daniel-hauser/homelab-rack/renders/beds/bed_6.png

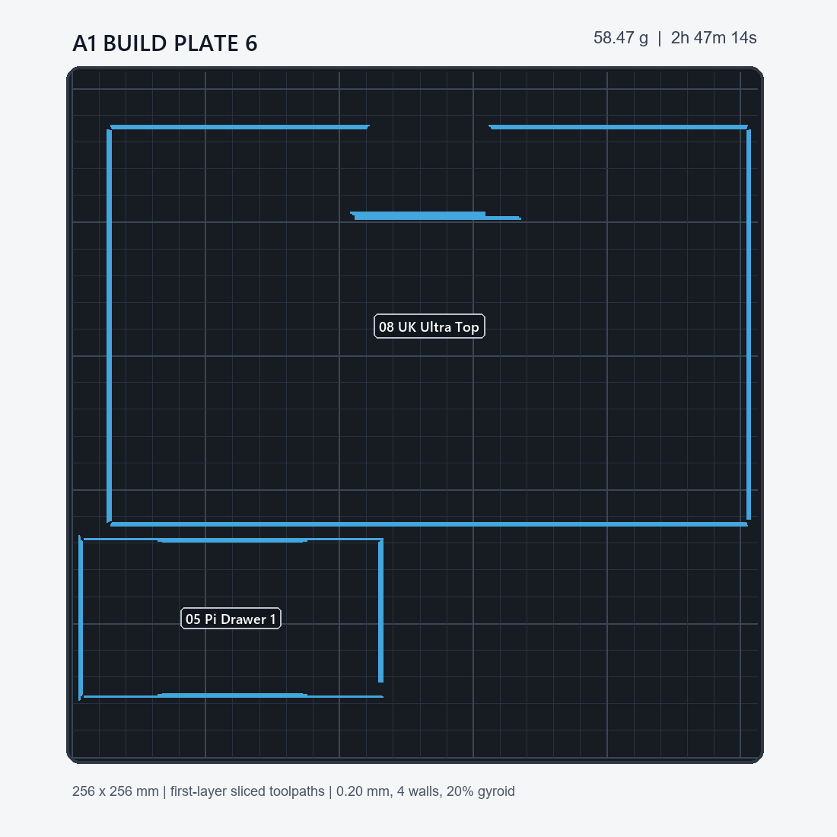
renders/beds/bed_6.png
