daniel-hauser/homelab-rack/renders/modular_bay_preview_final.png

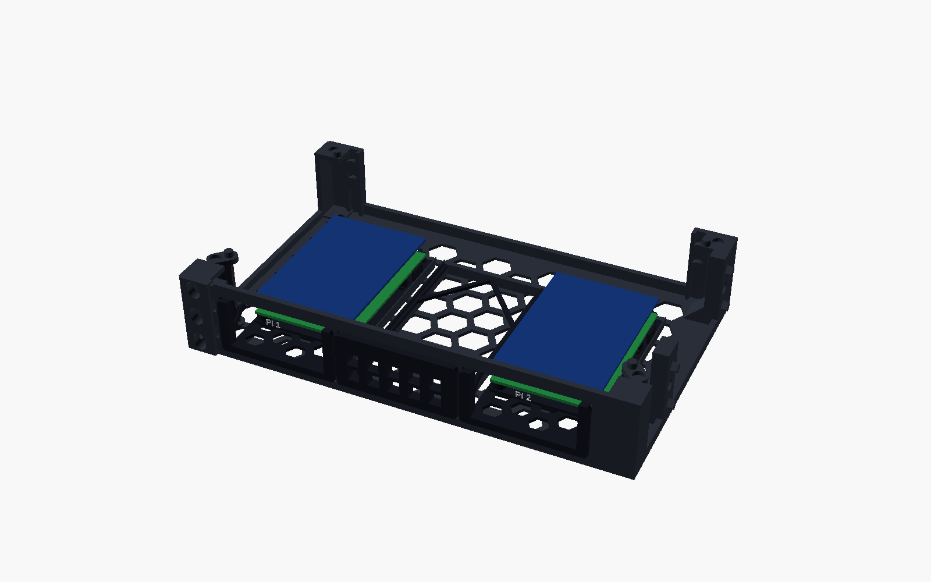
renders/modular_bay_preview_final.png
