daniel-hauser/homelab-rack/renders/rack_preview_final.png

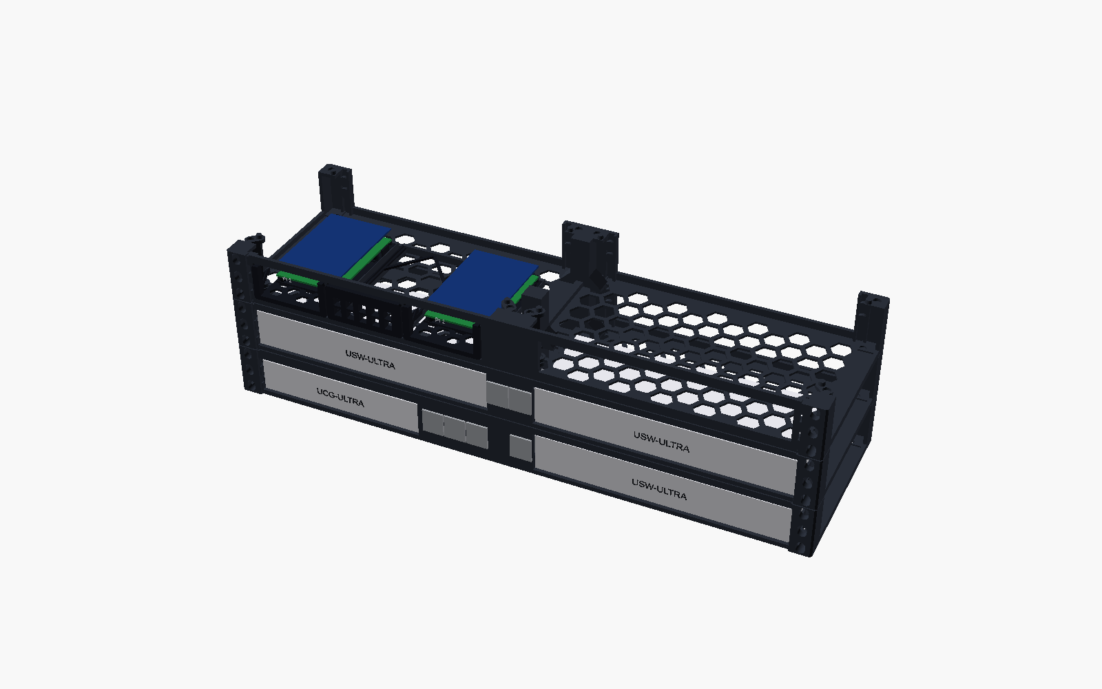
renders/rack_preview_final.png
