daniel-hauser/homelab-rack/renders/side_join_preview.png

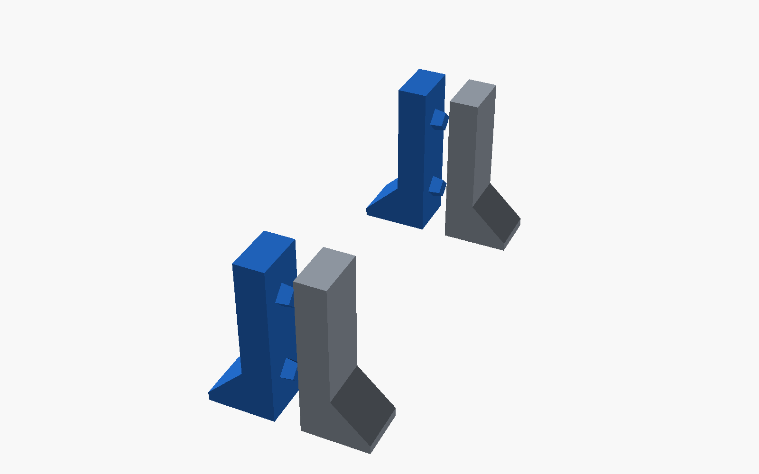
renders/side_join_preview.png
