daniel-hauser/homelab-rack/REVIEW_ONLY/Pi_Mount_Alternatives/A_Magnetic_Cradle_Cutaway.png

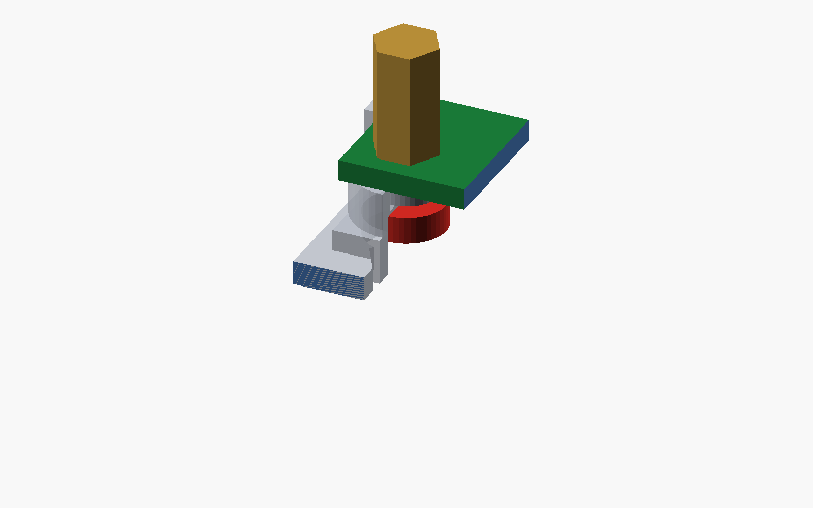
REVIEW_ONLY/Pi_Mount_Alternatives/A_Magnetic_Cradle_Cutaway.png
