daniel-hauser/homelab-rack/REVIEW_ONLY/Pi_Mount_Alternatives/A_Magnetic_Cradle_Underside.png

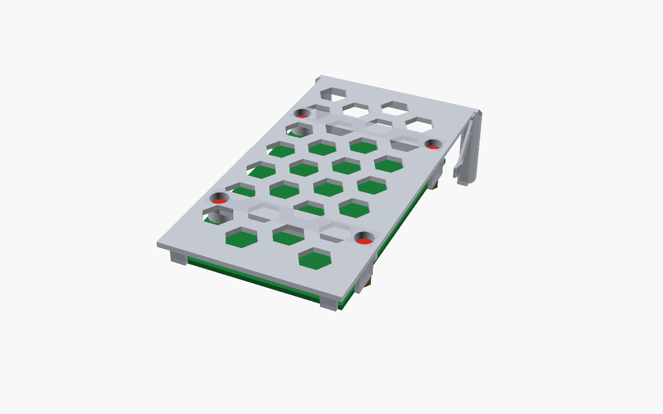
REVIEW_ONLY/Pi_Mount_Alternatives/A_Magnetic_Cradle_Underside.png
