daniel-hauser/homelab-rack/PRINT_THESE/TEST_FIRST/10_Seam_Tower_Female_Test.stl

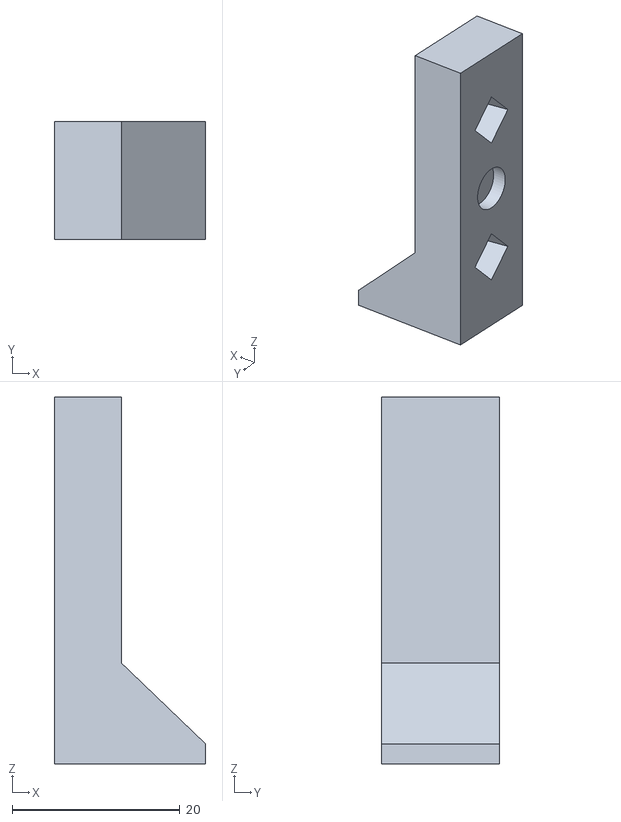
[picture p22: CAD file, 2026-09-30]
PRINT_THESE/TEST_FIRST/10_Seam_Tower_Female_Test.stl
18.0 x 14.0 x 43.7
