daniel-hauser/homelab-rack/PRINT_THESE/STLs/03_USW_Ultra_Right.stl

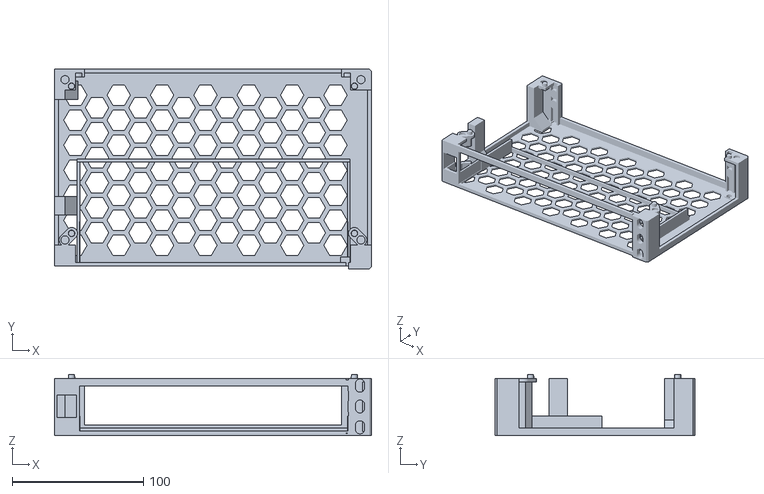
[picture p23: CAD file, 2026-09-30]
PRINT_THESE/STLs/03_USW_Ultra_Right.stl
241.3 x 152.0 x 46.7
