daniel-hauser/homelab-rack/PRINT_THESE/TEST_FIRST/04_Desktop_Feet_Set.stl

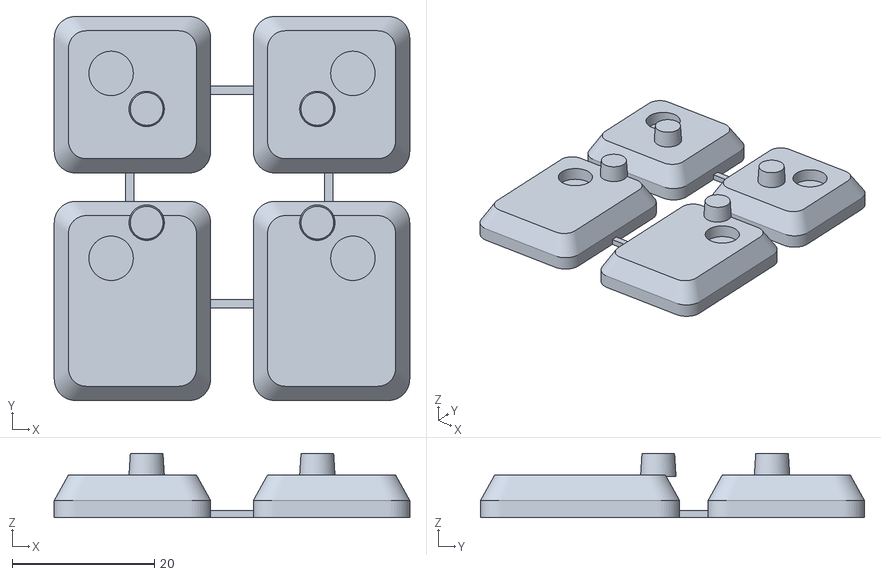
[picture p24: CAD file, 2026-09-30]
PRINT_THESE/TEST_FIRST/04_Desktop_Feet_Set.stl
50.0 x 54.0 x 9.00
