daniel-hauser/homelab-rack/PRINT_THESE/TEST_FIRST/01_Bay_Fit_Test.stl

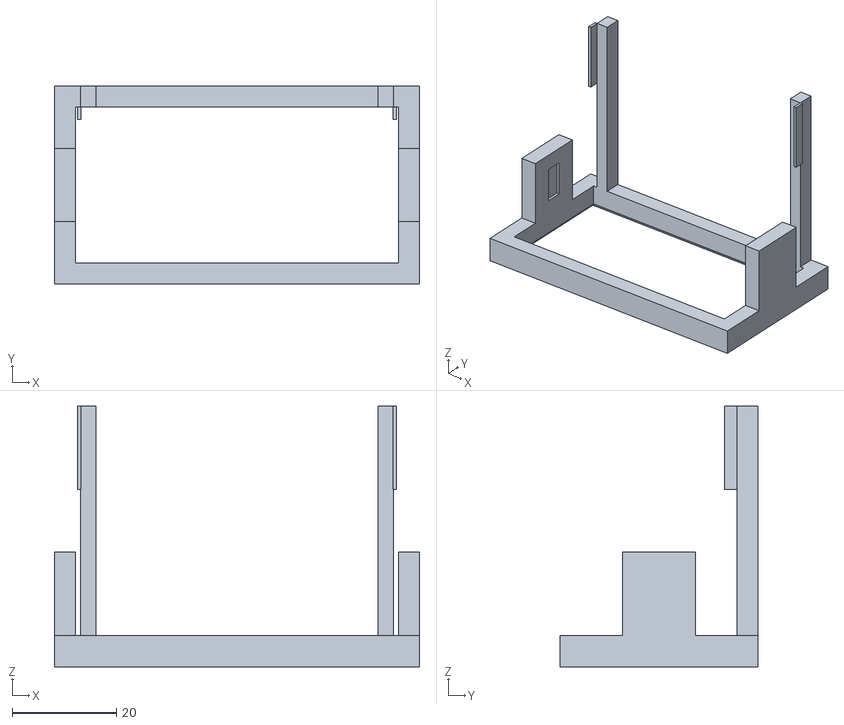
[picture p25: CAD file, 2026-09-30]
PRINT_THESE/TEST_FIRST/01_Bay_Fit_Test.stl
70.0 x 38.0 x 50.0
