daniel-hauser/homelab-rack/viewer/public/models/desktop_feet_installed.stl

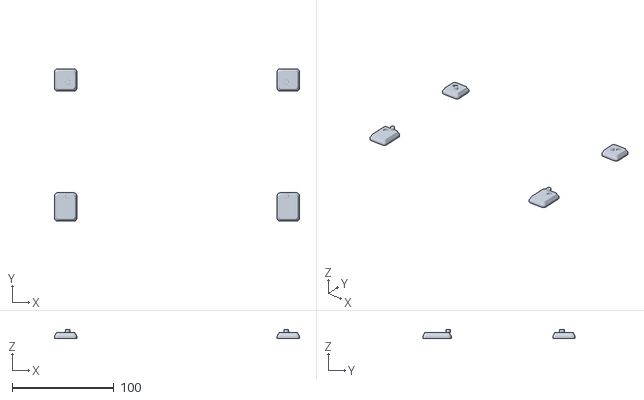
[picture p26: CAD file, 2026-09-30]
viewer/public/models/desktop_feet_installed.stl
241.3 x 150.0 x 9.00
