daniel-hauser/homelab-rack/PRINT_THESE/STLs/01_UCG_Ultra.stl

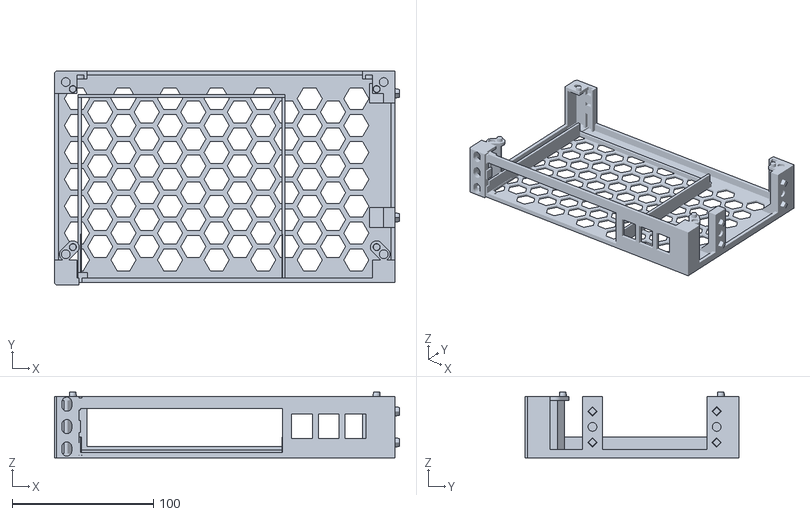
[picture p27: CAD file, 2026-09-30]
PRINT_THESE/STLs/01_UCG_Ultra.stl
244.5 x 152.0 x 46.7
