daniel-hauser/homelab-rack/PRINT_THESE/TEST_FIRST/07_Magnet_Polarity_Key.stl

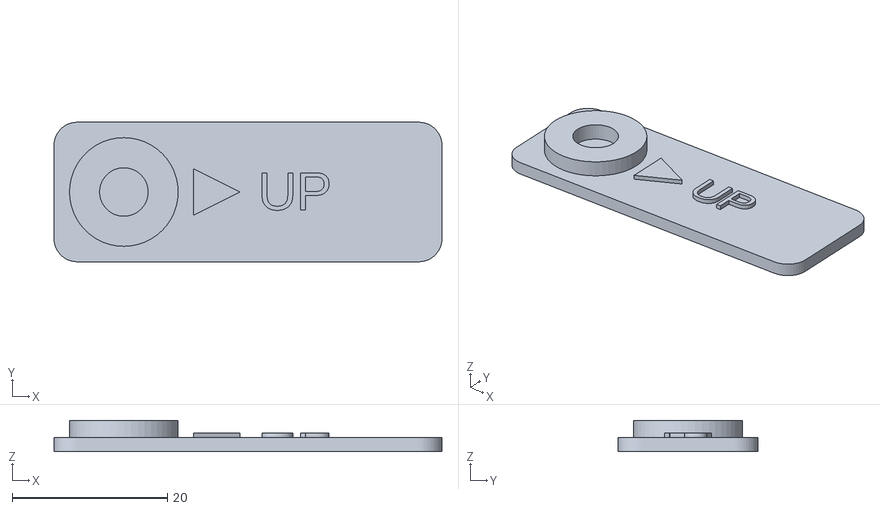
[picture p28: CAD file, 2026-09-30]
PRINT_THESE/TEST_FIRST/07_Magnet_Polarity_Key.stl
50.0 x 18.0 x 4.00
