daniel-hauser/homelab-rack/PRINT_THESE/TEST_FIRST/09_Seam_Tower_Male_Test.stl

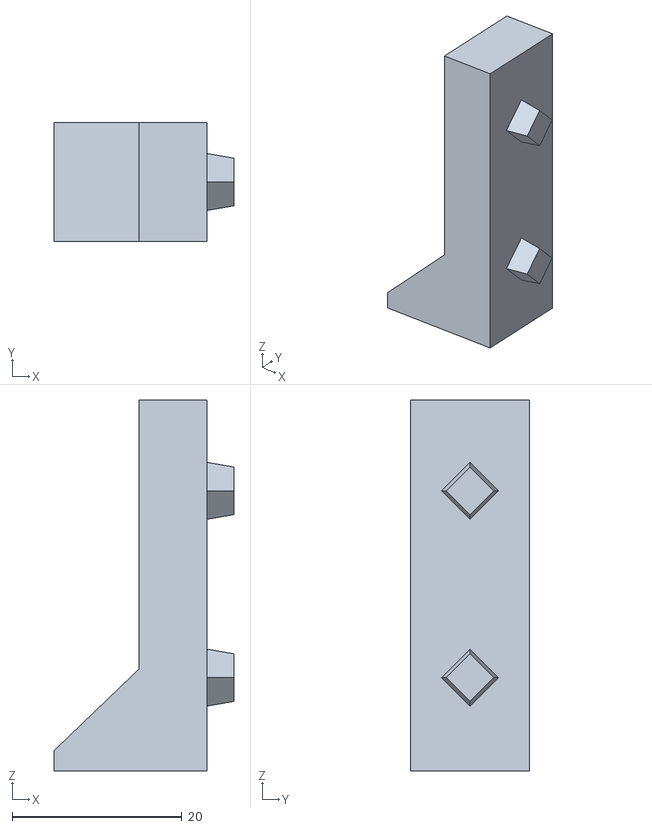
[picture p29: CAD file, 2026-09-30]
PRINT_THESE/TEST_FIRST/09_Seam_Tower_Male_Test.stl
21.2 x 14.0 x 43.7
