daniel-hauser/homelab-rack/PRINT_THESE/STLs/09_Rear_Spine_A.stl

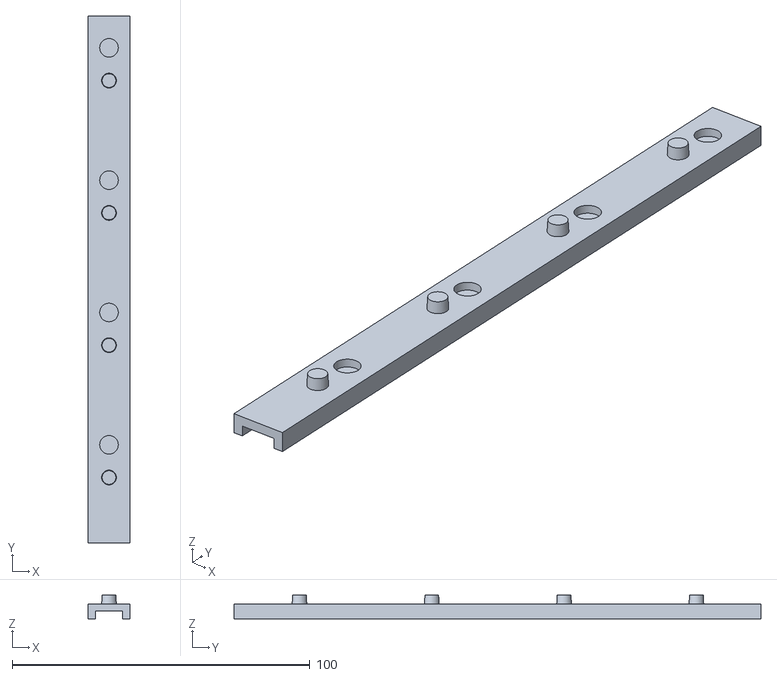
[picture p30: CAD file, 2026-09-30]
PRINT_THESE/STLs/09_Rear_Spine_A.stl
14.0 x 177.1 x 8.00
