daniel-hauser/homelab-rack/PRINT_THESE/TEST_FIRST/08_Rack_Ear_Test.stl

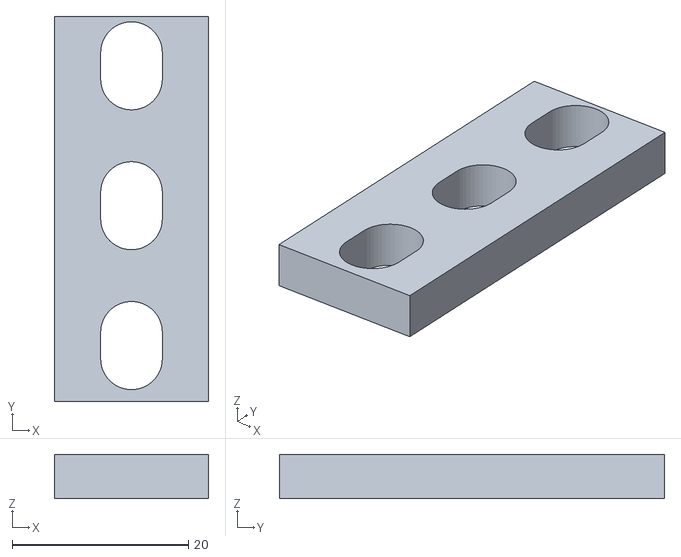
[picture p31: CAD file, 2026-09-30]
PRINT_THESE/TEST_FIRST/08_Rack_Ear_Test.stl
17.5 x 43.7 x 5.00
