daniel-hauser/homelab-rack/renders/beds-no-test/all_beds.png

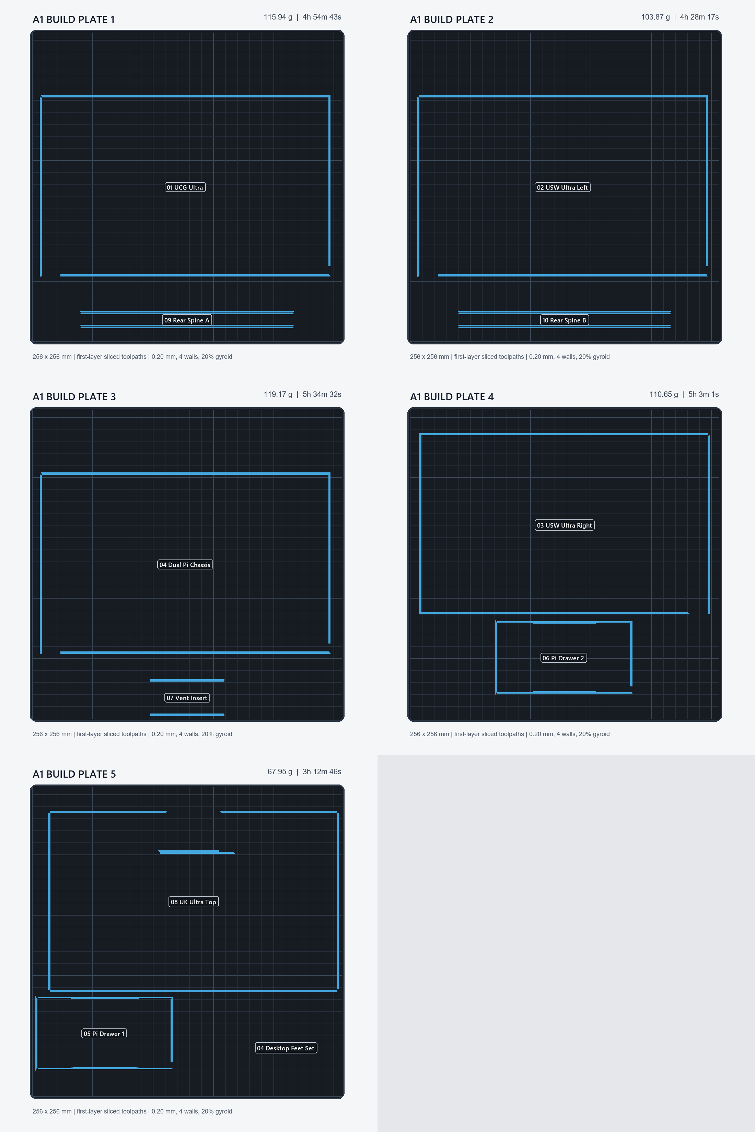
renders/beds-no-test/all_beds.png
