daniel-hauser/homelab-rack/renders/beds-no-test/bed_3.png

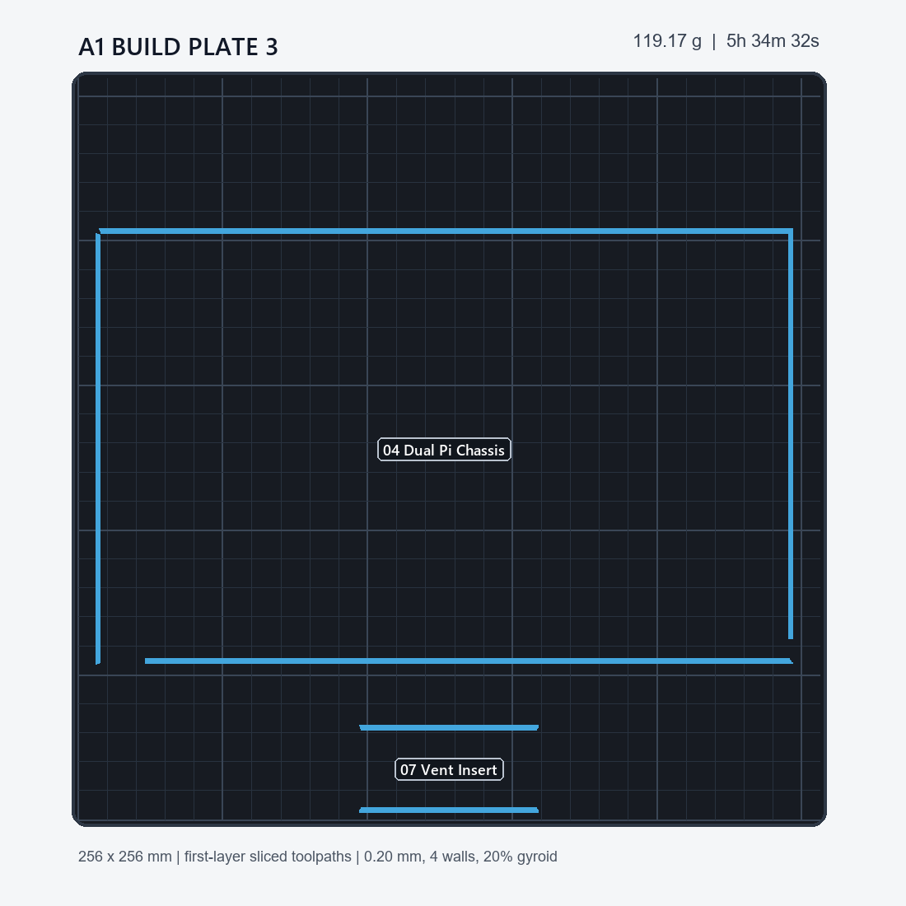
renders/beds-no-test/bed_3.png
