daniel-hauser/homelab-rack/renders/beds-no-test/bed_4.png

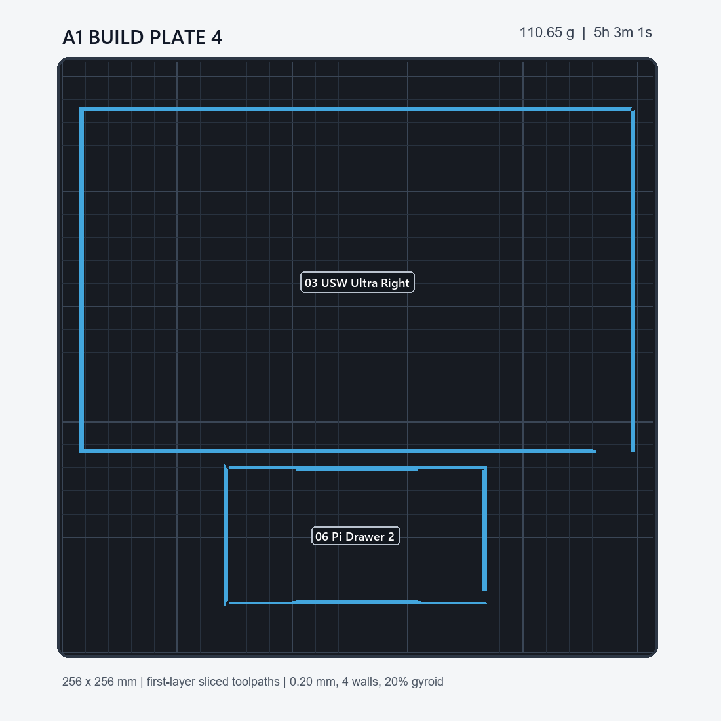
renders/beds-no-test/bed_4.png
