daniel-hauser/homelab-rack/renders/production_test_plate.png

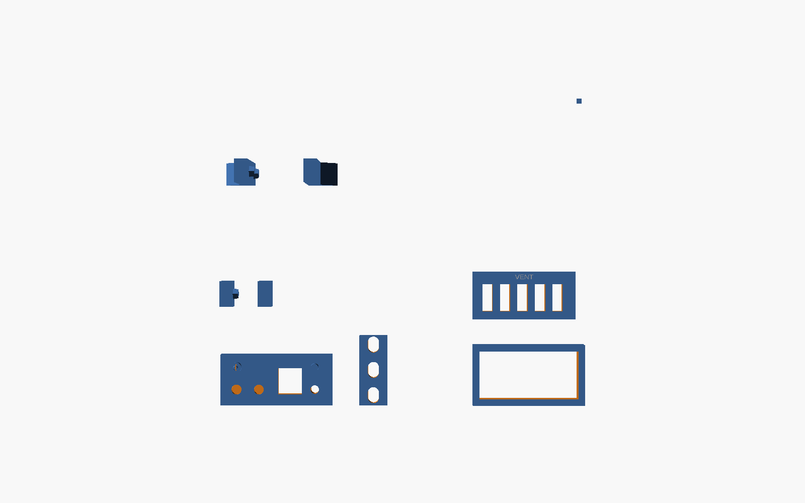
renders/production_test_plate.png
